SeanP2001/Sunrise_Alarm_Clock_V2/Images/Display.jpg

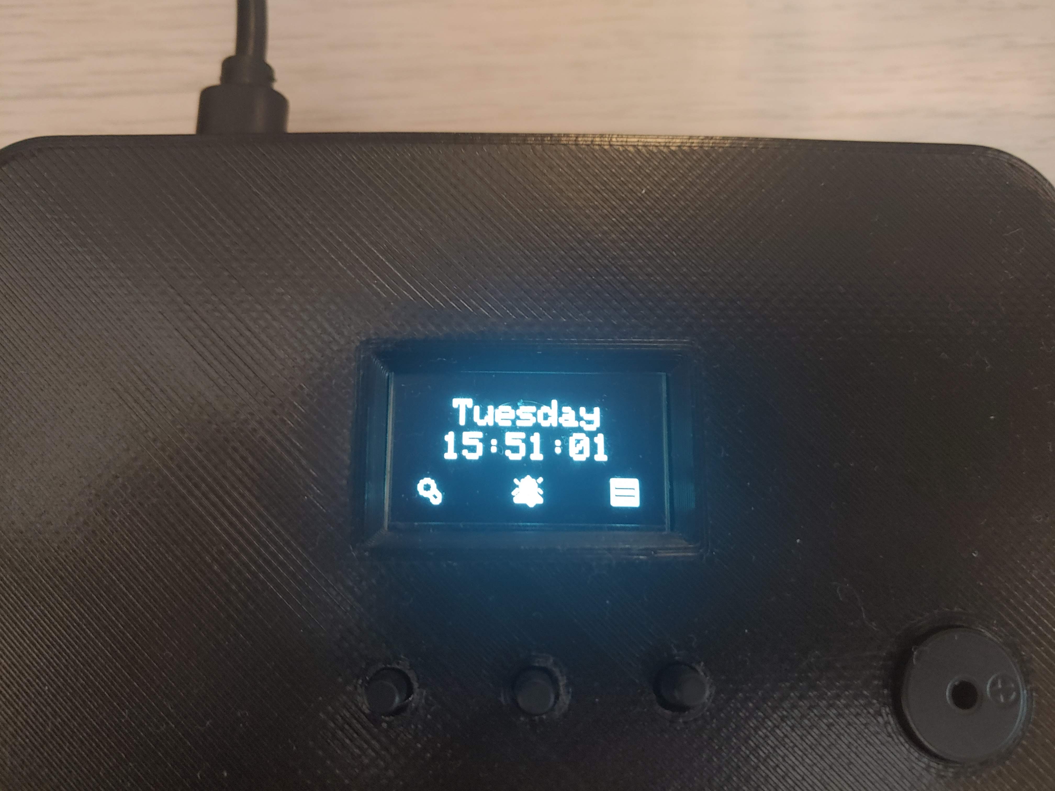
Images/Display.jpg
