SeanP2001/Sunrise_Alarm_Clock_V2/Code/Sunrise_Alarm_Clock_V2/Icons.h

// 'lightOffIcon', 16x16px
const unsigned char lightOffIcon [] PROGMEM = {
  0x00, 0x00, 0x00, 0x00, 0x07, 0x00, 0x1d, 0xc0, 0x10, 0x40, 0x30, 0x60, 0x20, 0x20, 0x30, 0x60, 
  0x10, 0x70, 0x1d, 0xd8, 0x07, 0x8c, 0x00, 0x84, 0x00, 0x44, 0x00, 0x6c, 0x00, 0x38, 0x00, 0x00
};

// 'lightOnIcon', 16x16px
const unsigned char lightOnIcon [] PROGMEM = {
  0x00, 0x20, 0x00, 0x20, 0x07, 0x00, 0x1f, 0xcc, 0x1f, 0xc0, 0x3f, 0xe0, 0x3f, 0xe0, 0x3f, 0xe0, 
  0x1f, 0xf0, 0x5f, 0xd8, 0x87, 0x8c, 0x00, 0x84, 0x08, 0x44, 0x10, 0x6c, 0x00, 0x38, 0x00, 0x00
};

// 'alarmOffIcon', 16x16px
const unsigned char alarmOffIcon [] PROGMEM = {
  0x00, 0x80, 0x01, 0xc0, 0x07, 0x70, 0x04, 0x10, 0x0c, 0x18, 0x08, 0x08, 0x08, 0x08, 0x08, 0x08, 
  0x08, 0x08, 0x08, 0x08, 0x18, 0x0c, 0x30, 0x06, 0x60, 0x03, 0x7f, 0xff, 0x00, 0xf0, 0x00, 0x60
};

// 'alarmOnIcon', 16x16px
const unsigned char alarmOnIcon [] PROGMEM = {
  0x00, 0x80, 0x01, 0xc1, 0x47, 0xf2, 0x27, 0xf0, 0x0f, 0xf8, 0x0f, 0xf8, 0x0f, 0xf8, 0x2f, 0xfa, 
  0x4f, 0xf9, 0x8f, 0xf8, 0x1f, 0xfc, 0x3f, 0xfe, 0x7f, 0xff, 0x7f, 0xff, 0x00, 0xf0, 0x00, 0x60
};

// 'Menu_Icon', 16x16px
const unsigned char menuIcon [] PROGMEM = {
  0x00, 0x00, 0x7f, 0xfe, 0x40, 0x02, 0x5f, 0xfa, 0x5f, 0xfa, 0x40, 0x02, 0x40, 0x02, 0x5f, 0xfa, 
  0x5f, 0xfa, 0x40, 0x02, 0x40, 0x02, 0x5f, 0xfa, 0x5f, 0xfa, 0x40, 0x02, 0x7f, 0xfe, 0x00, 0x00
};

// 'upArrowIcon', 16x16px
const unsigned char upArrowIcon [] PROGMEM = {
  0x01, 0x80, 0x03, 0xc0, 0x07, 0xe0, 0x0f, 0xf0, 0x1f, 0xf8, 0x3f, 0xfc, 0x7f, 0xfe, 0xff, 0xff, 
  0x07, 0xe0, 0x07, 0xe0, 0x07, 0xe0, 0x07, 0xe0, 0x07, 0xe0, 0x07, 0xe0, 0x07, 0xe0, 0x07, 0xe0
};

// 'downArrowIcon', 16x16px
const unsigned char downArrowIcon [] PROGMEM = {
  0x07, 0xe0, 0x07, 0xe0, 0x07, 0xe0, 0x07, 0xe0, 0x07, 0xe0, 0x07, 0xe0, 0x07, 0xe0, 0x07, 0xe0, 
  0xff, 0xff, 0x7f, 0xfe, 0x3f, 0xfc, 0x1f, 0xf8, 0x0f, 0xf0, 0x07, 0xe0, 0x03, 0xc0, 0x01, 0x80
};
